elubeck/RoboScope2/PipetRobot/pipettorUpsideDown.png

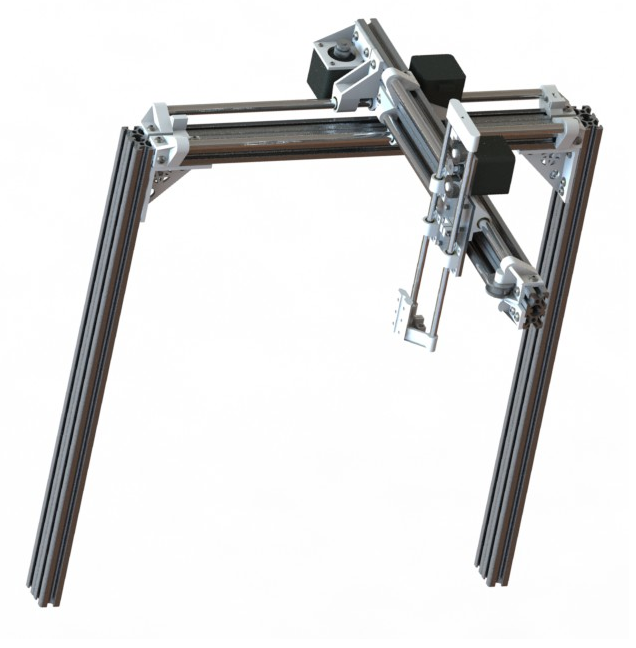
PipetRobot/pipettorUpsideDown.png
