elubeck/RoboScope2/PipetRobot/upsideDown2.JPG

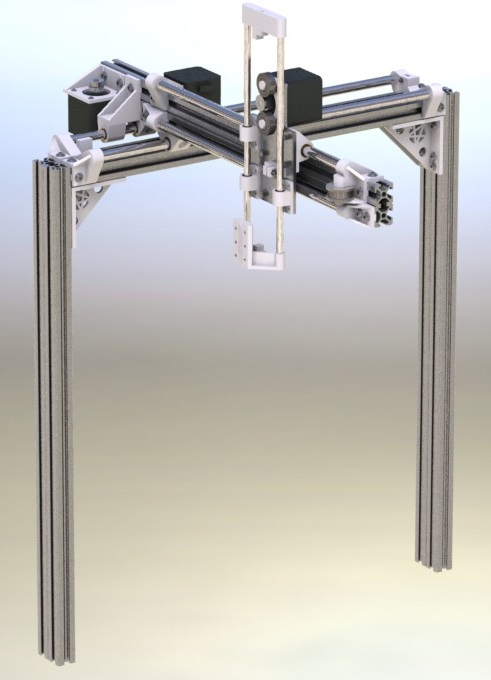
PipetRobot/upsideDown2.JPG
