elubeck/RoboScope2/PipetRobot/NeedleLuerHolder.sldasm

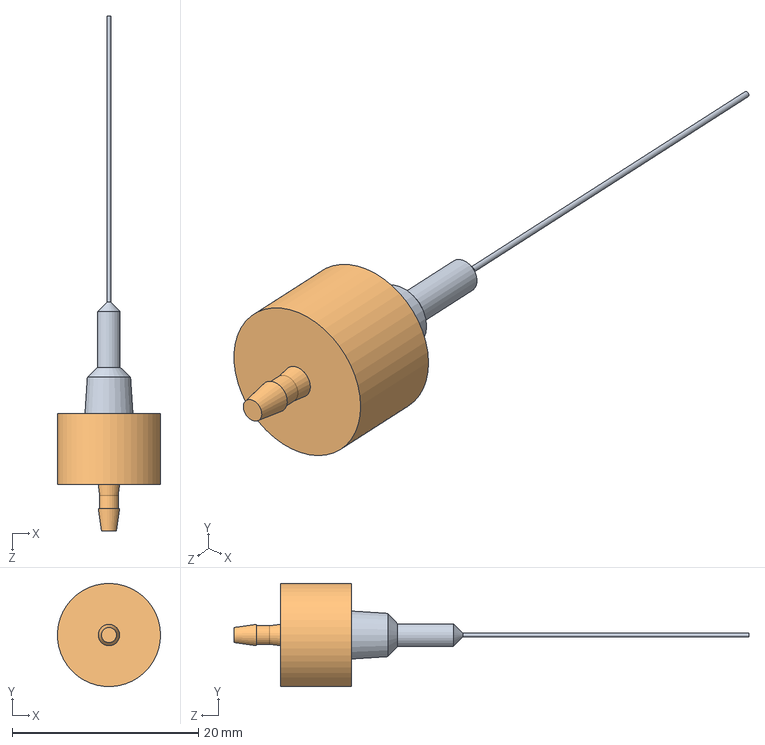
[picture p13: CAD file, 2014-07-27]
PipetRobot/NeedleLuerHolder.sldasm
11.1 x 11.1 x 55.3 mm
needleluer
needle
