elubeck/RoboScope2/PipetRobot/xaxisbearing.STL

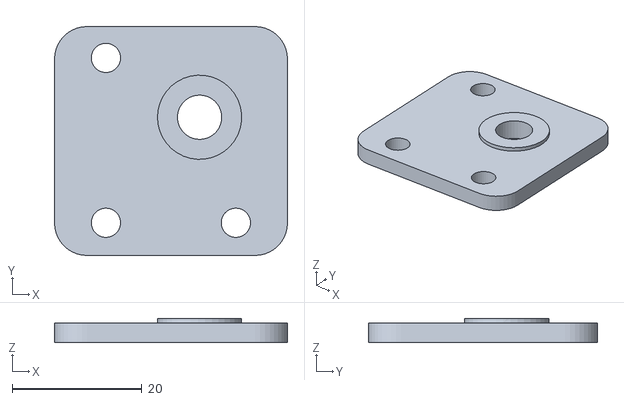
[picture p20: CAD file, 2014-07-27]
PipetRobot/xaxisbearing.STL
35.9 x 35.2 x 3.70
