elubeck/RoboScope2/PipetRobot/bearingmountflat.sldprt

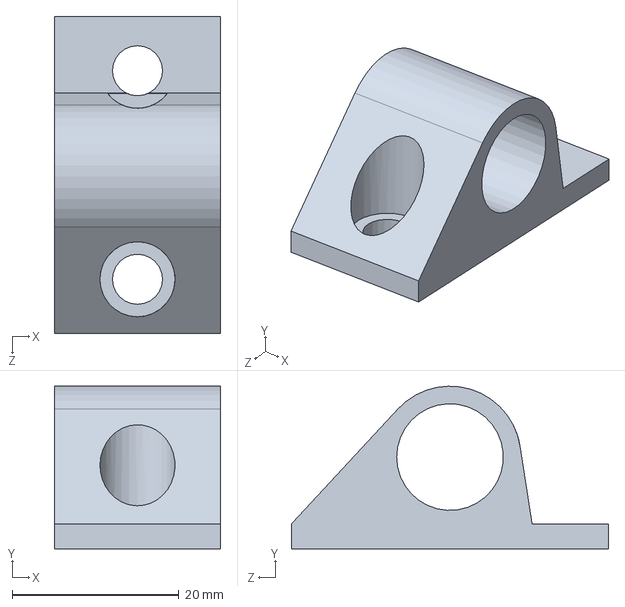
[picture p21: CAD file, 2014-07-27]
PipetRobot/bearingmountflat.sldprt
19.9 x 19.5 x 38.0 mm
