elubeck/RoboScope2/PipetRobot/syringe/syringeholderbottom.sldprt

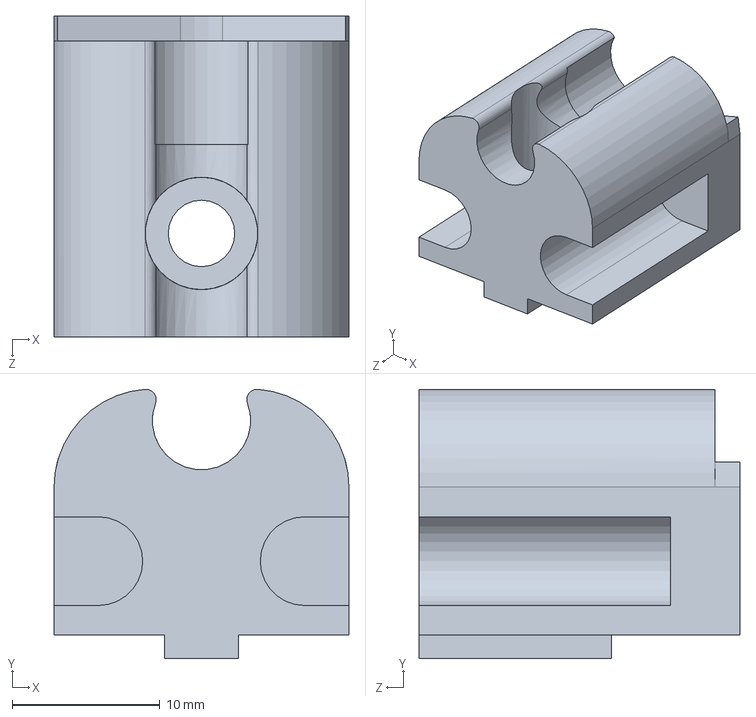
[picture p22: CAD file, 2014-07-27]
PipetRobot/syringe/syringeholderbottom.sldprt
20.0 x 18.2 x 21.7 mm
