elubeck/RoboScope2/PipetRobot/vialholder/bottle.SLDPRT

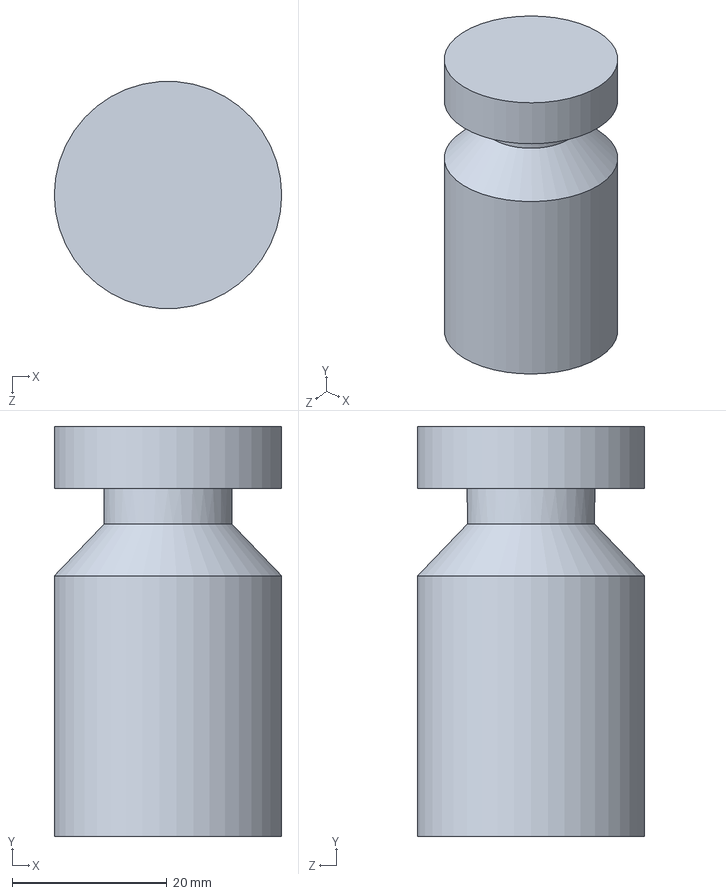
[picture p23: CAD file, 2014-07-27]
PipetRobot/vialholder/bottle.SLDPRT
29.4 x 53.0 x 29.3 mm
