elubeck/RoboScope2/PipetRobot/vialholder/vialrack.SLDPRT

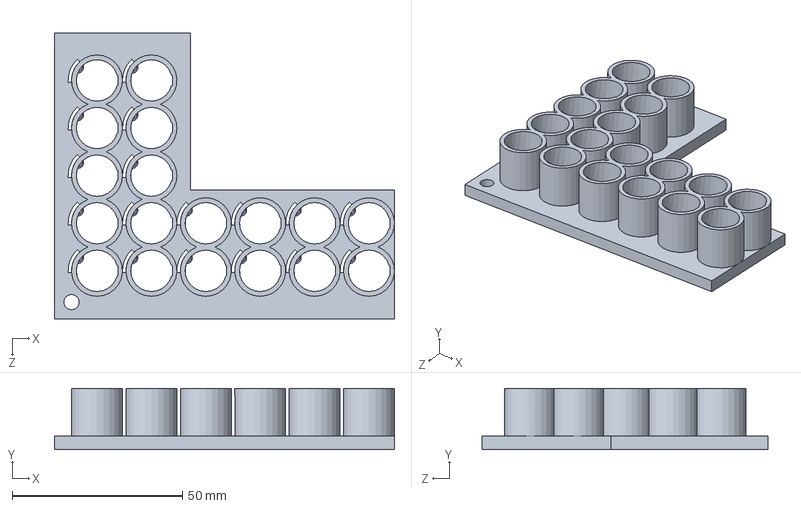
[picture p24: CAD file, 2014-07-27]
PipetRobot/vialholder/vialrack.SLDPRT
100.0 x 18.0 x 84.2 mm
