elubeck/RoboScope2/PipetRobot/syringe/plungerholder.STL

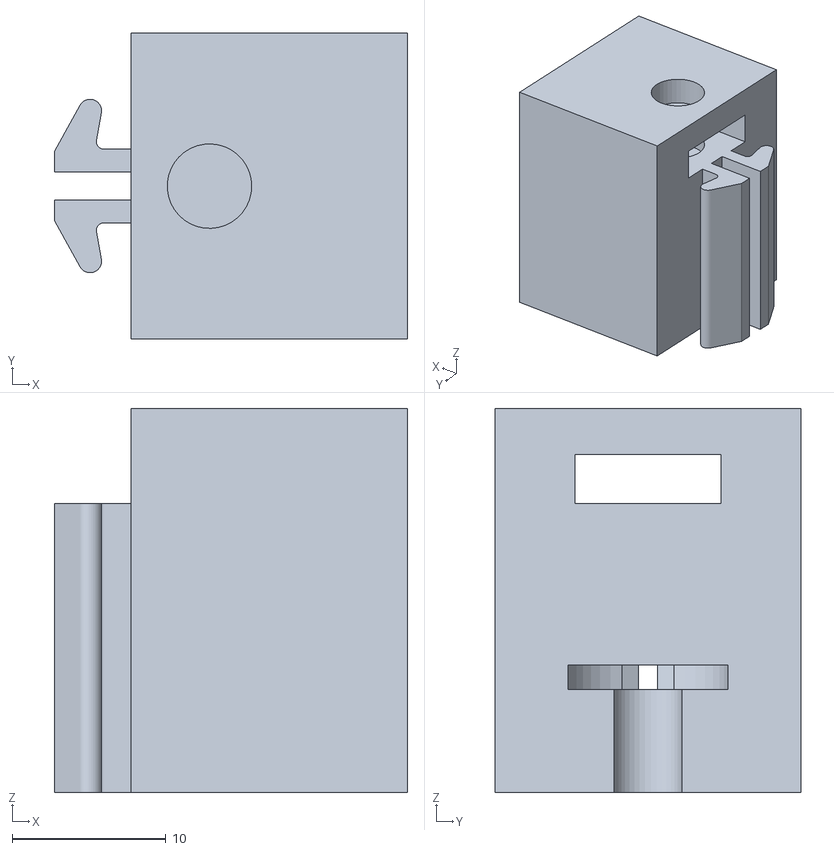
[picture p25: CAD file, 2014-07-27]
PipetRobot/syringe/plungerholder.STL
23.0 x 20.0 x 25.0
