elubeck/RoboScope2/PipetRobot/vialholder/bottlerack.SLDPRT

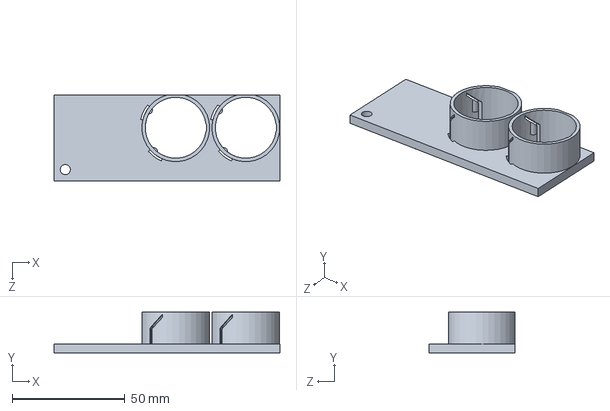
[picture p26: CAD file, 2014-07-27]
PipetRobot/vialholder/bottlerack.SLDPRT
100.0 x 18.0 x 38.0 mm
