elubeck/RoboScope2/PipetRobot/syringe/pistonholder.sldprt

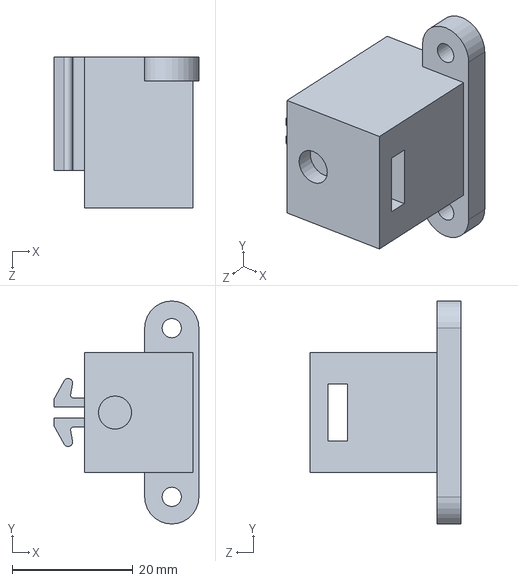
[picture p27: CAD file, 2014-07-27]
PipetRobot/syringe/pistonholder.sldprt
24.0 x 37.0 x 25.0 mm
