elubeck/RoboScope2/PipetRobot/vialholder/1_6mltube.SLDPRT

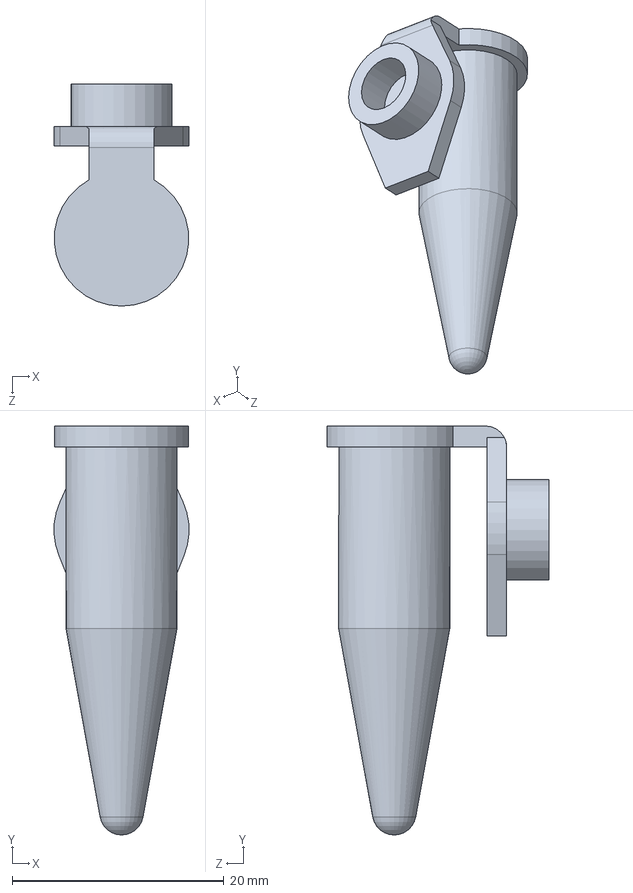
[picture p28: CAD file, 2014-07-27]
PipetRobot/vialholder/1_6mltube.SLDPRT
12.7 x 38.6 x 21.0 mm
