elubeck/RoboScope2/PipetRobot/CornerRodClampCutout.sldprt

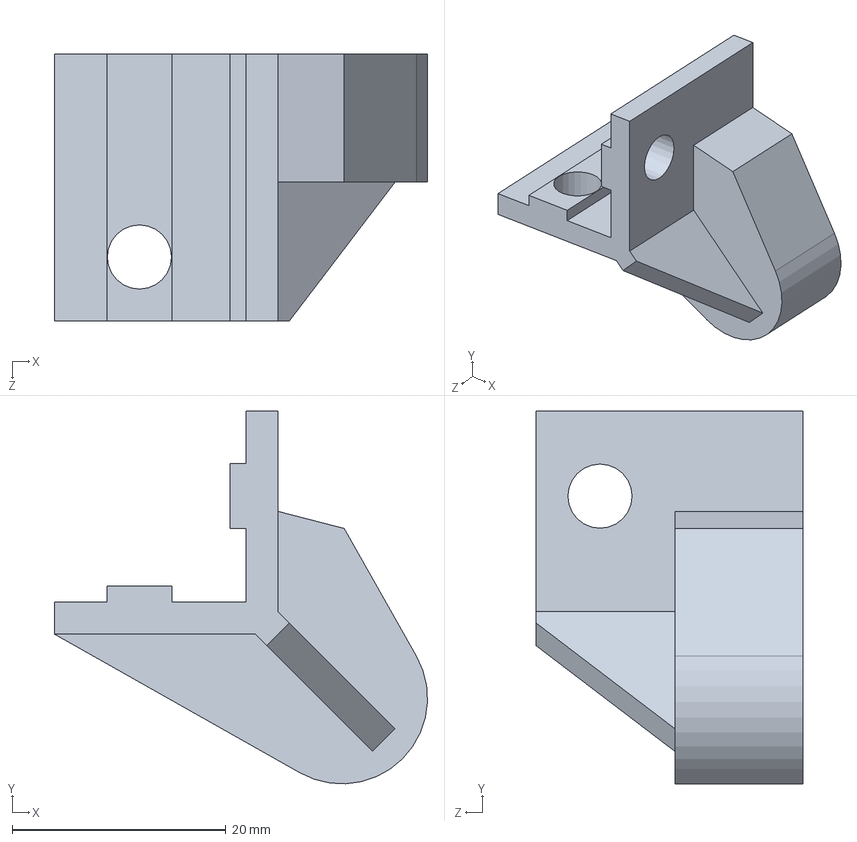
[picture p29: CAD file, 2014-07-27]
PipetRobot/CornerRodClampCutout.sldprt
34.9 x 34.8 x 25.0 mm
