elubeck/RoboScope2/PipetRobot/syringe/rodcoupler.sldprt

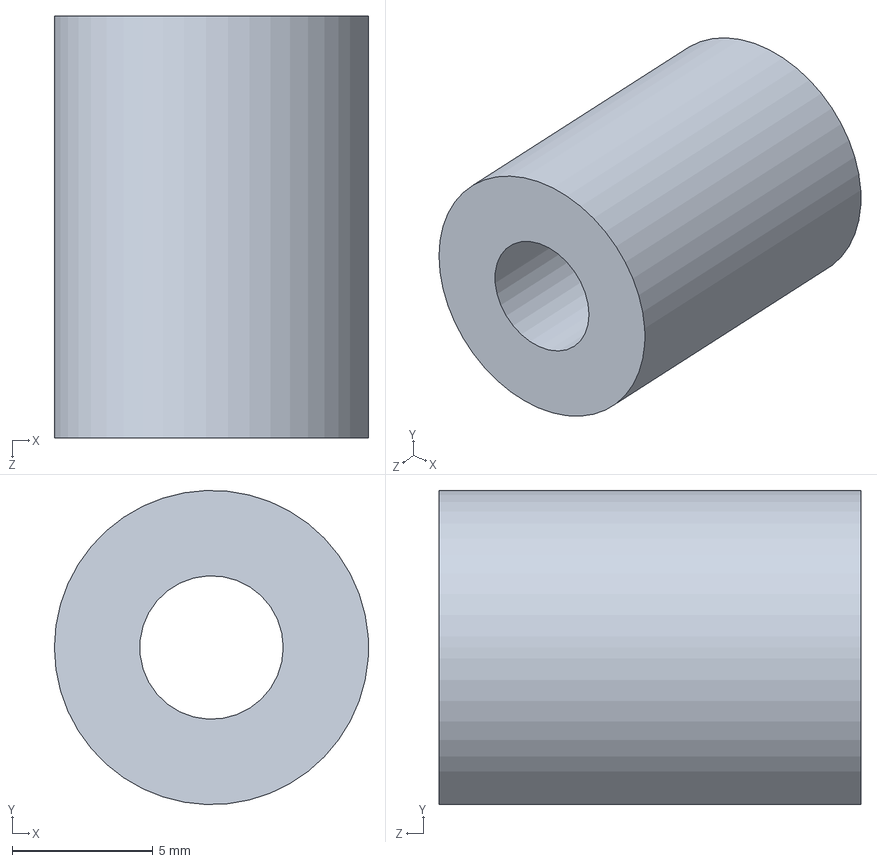
[picture p30: CAD file, 2014-07-27]
PipetRobot/syringe/rodcoupler.sldprt
11.2 x 11.2 x 15.0 mm
