elubeck/RoboScope2/PipetRobot/beltTrapTensioner2.sldprt

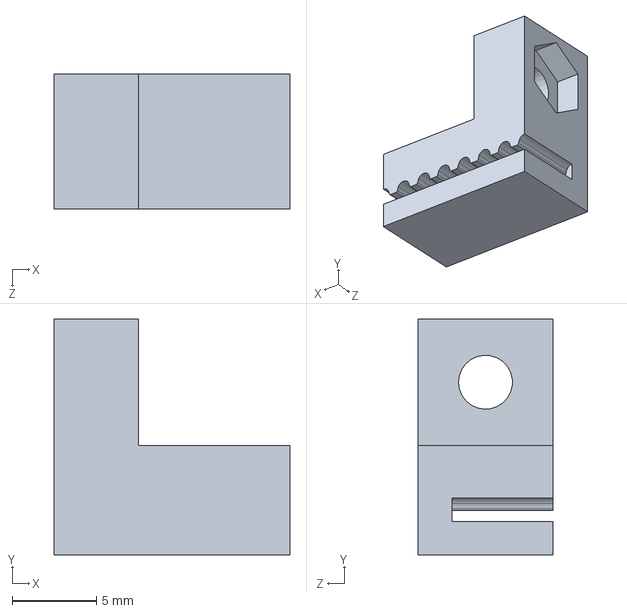
[picture p31: CAD file, 2014-07-27]
PipetRobot/beltTrapTensioner2.sldprt
14.0 x 14.0 x 8.00 mm
