elubeck/RoboScope2/PipetRobot/beltTrapmid.STL

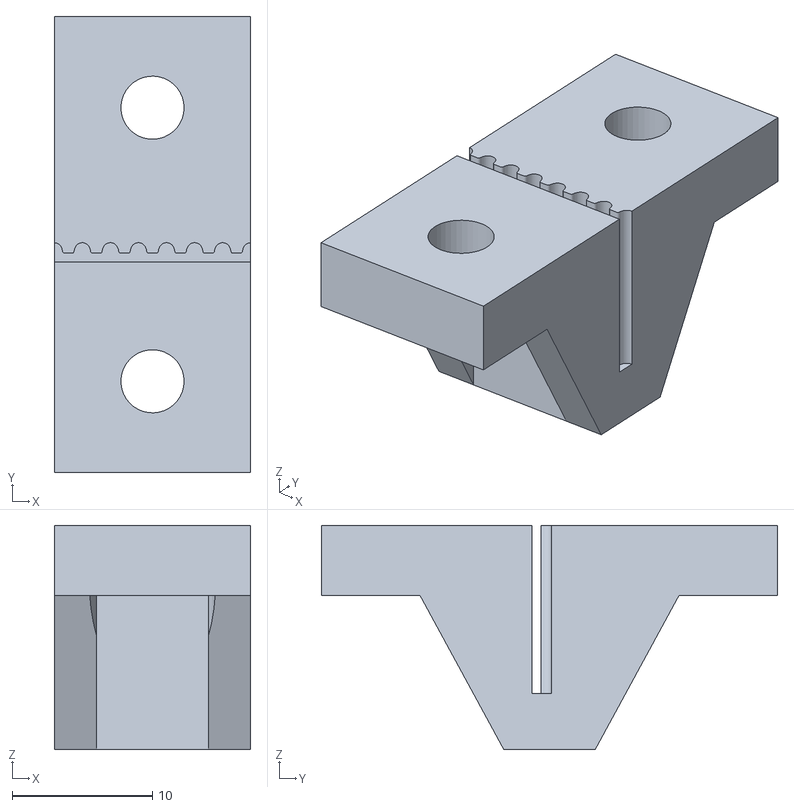
[picture p32: CAD file, 2014-07-27]
PipetRobot/beltTrapmid.STL
14.0 x 32.5 x 16.0
