elubeck/RoboScope2/PipetRobot/syringe/syringeplunger.SLDPRT

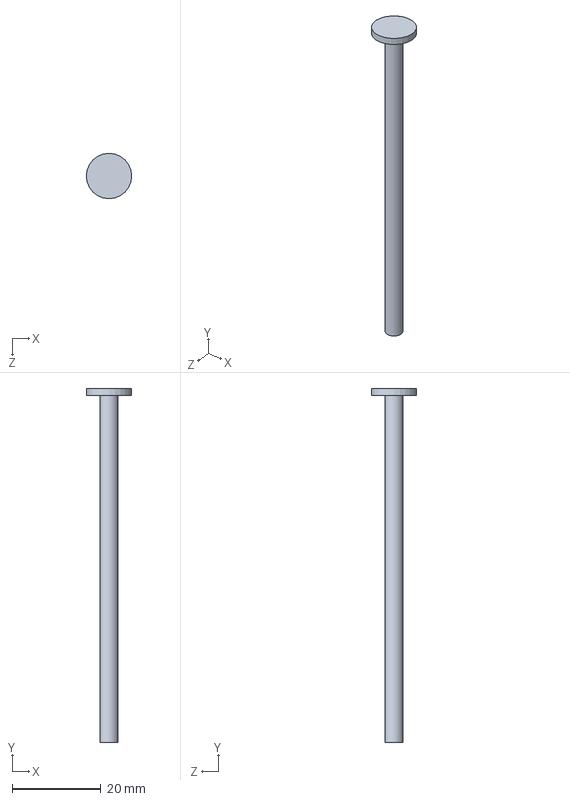
[picture p33: CAD file, 2014-07-27]
PipetRobot/syringe/syringeplunger.SLDPRT
10.2 x 79.6 x 10.2 mm
