elubeck/RoboScope2/PipetRobot/AluminumExtrusion.sldprt

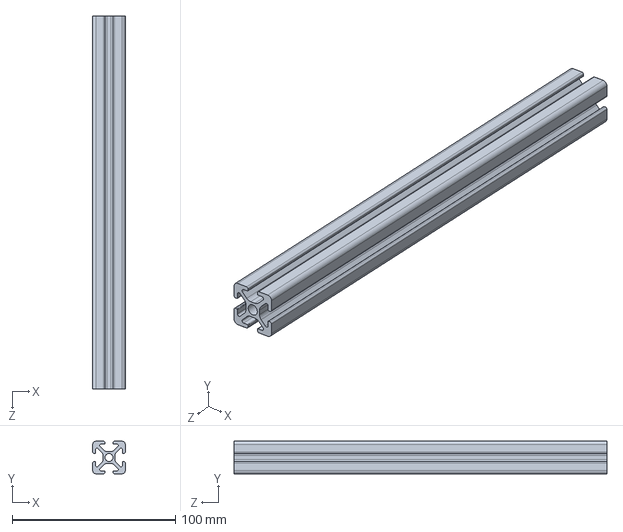
[picture p34: CAD file, 2014-07-27]
PipetRobot/AluminumExtrusion.sldprt
20.0 x 20.0 x 228.6 mm
