elubeck/RoboScope2/PipetRobot/syringe/needleluer.SLDPRT

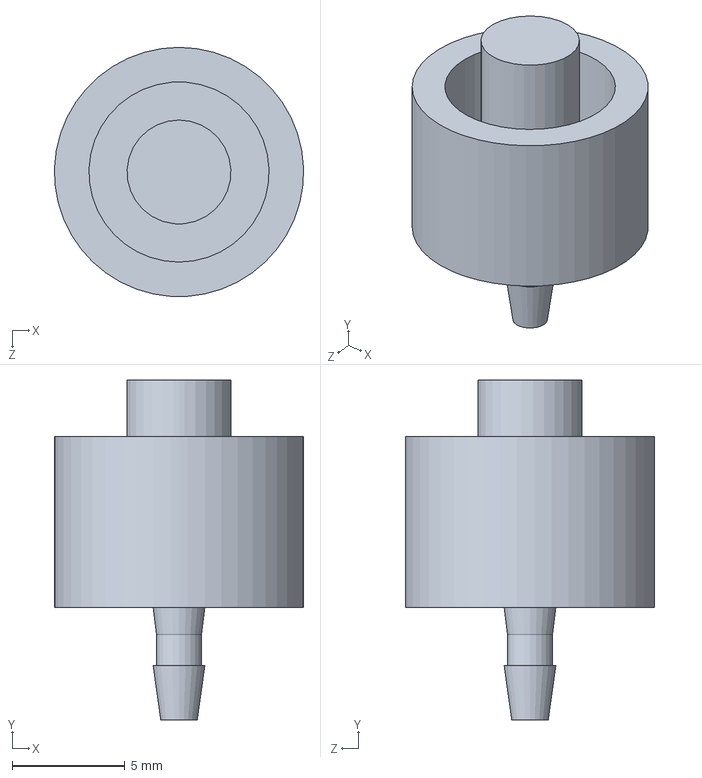
[picture p35: CAD file, 2014-07-27]
PipetRobot/syringe/needleluer.SLDPRT
11.1 x 15.1 x 11.1 mm
