elubeck/RoboScope2/PipetRobot/syringe/syringeclamper.sldprt

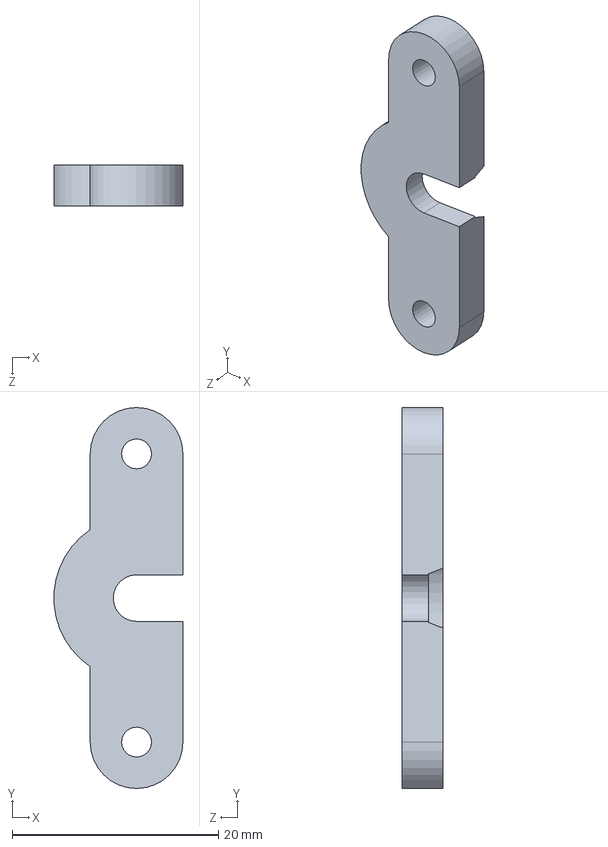
[picture p36: CAD file, 2014-07-27]
PipetRobot/syringe/syringeclamper.sldprt
12.5 x 37.0 x 4.00 mm
