elubeck/RoboScope2/PipetRobot/pulleymount.STL

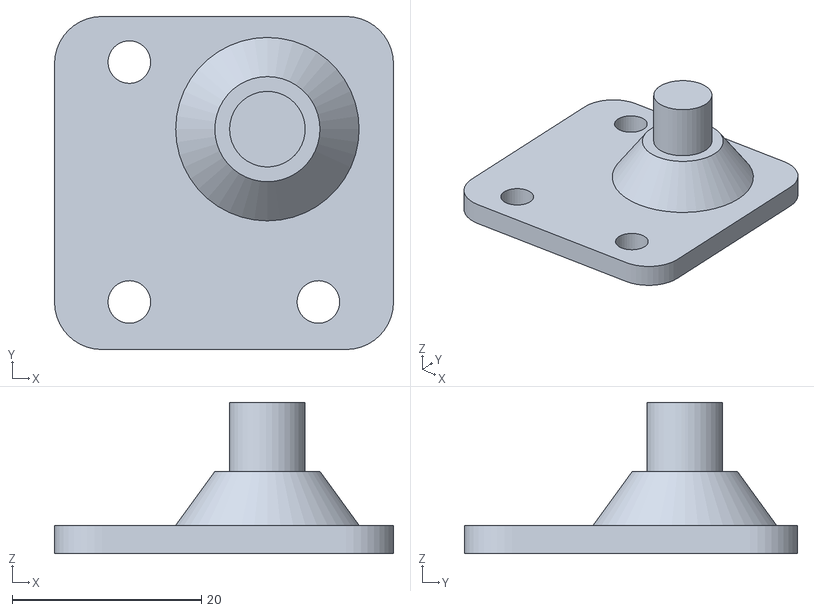
[picture p37: CAD file, 2014-07-27]
PipetRobot/pulleymount.STL
35.9 x 35.2 x 16.0
