elubeck/RoboScope2/PipetRobot/syringe/1mlsyringe.sldprt

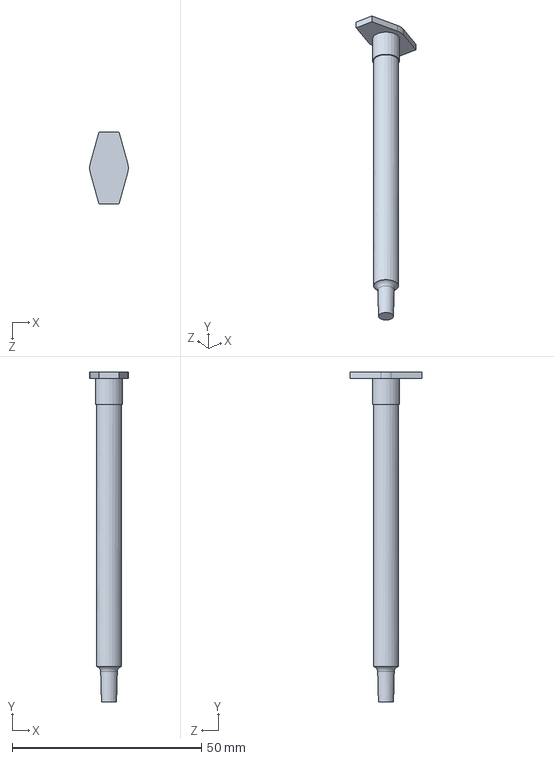
[picture p38: CAD file, 2014-07-27]
PipetRobot/syringe/1mlsyringe.sldprt
10.2 x 87.1 x 19.0 mm
