elubeck/RoboScope2/PipetRobot/syringe/syringeholdertop.sldprt

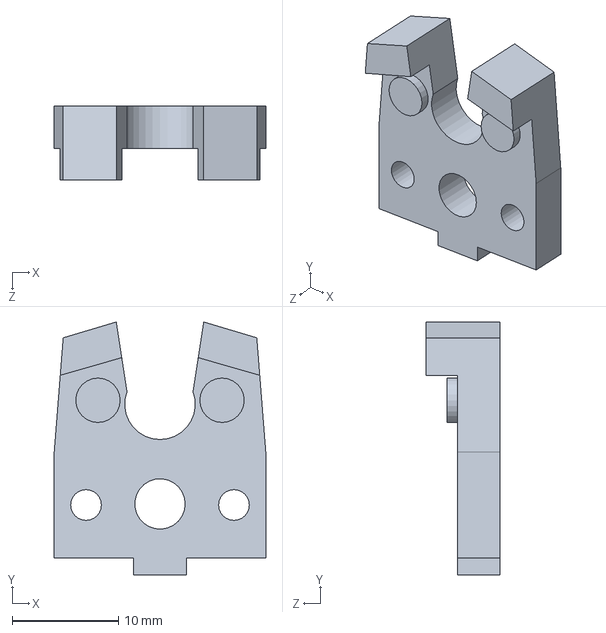
[picture p39: CAD file, 2014-07-27]
PipetRobot/syringe/syringeholdertop.sldprt
20.0 x 23.9 x 7.00 mm
