elubeck/RoboScope2/PipetRobot/beltTrapTensioner.sldprt

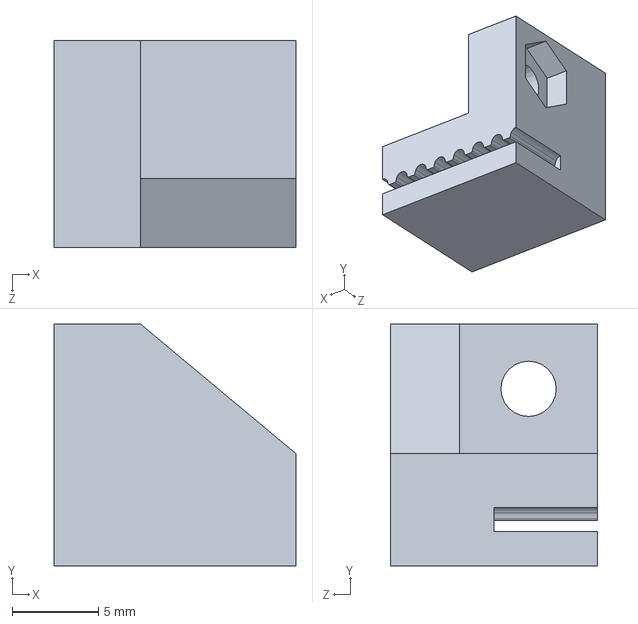
[picture p40: CAD file, 2014-07-27]
PipetRobot/beltTrapTensioner.sldprt
14.0 x 14.0 x 12.0 mm
