elubeck/RoboScope2/PipetRobot/syringe/needle.SLDPRT

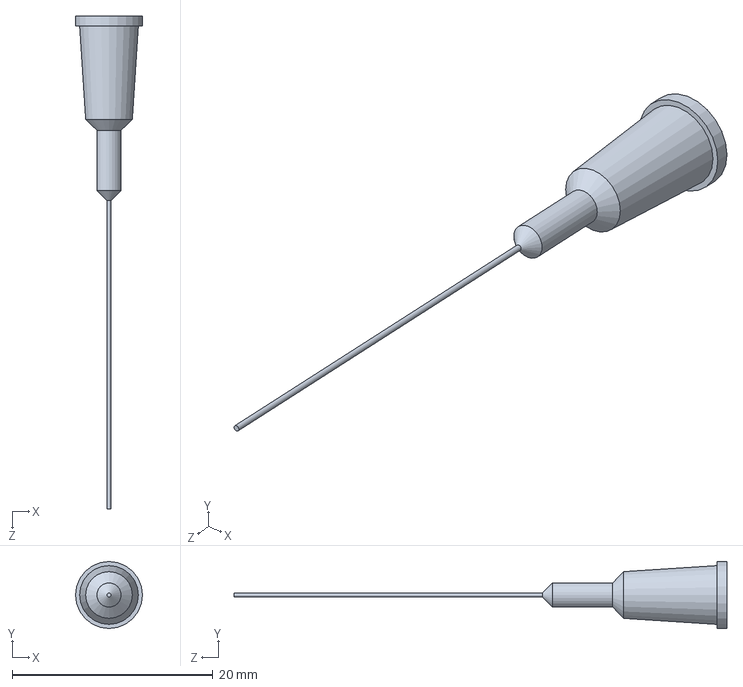
[picture p41: CAD file, 2014-07-27]
PipetRobot/syringe/needle.SLDPRT
6.67 x 6.67 x 49.1 mm
