elubeck/RoboScope2/PipetRobot/zsyringemount.sldprt

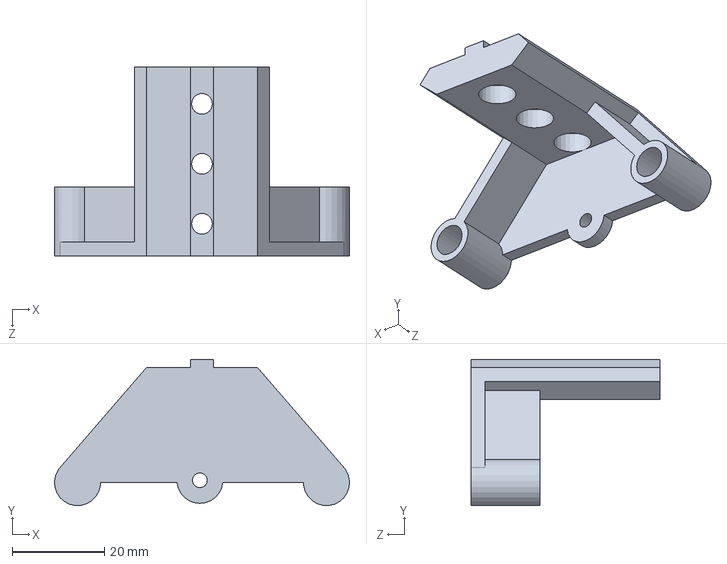
[picture p42: CAD file, 2014-07-27]
PipetRobot/zsyringemount.sldprt
64.0 x 31.7 x 41.0 mm
