elubeck/RoboScope2/PipetRobot/rainP200.SLDPRT

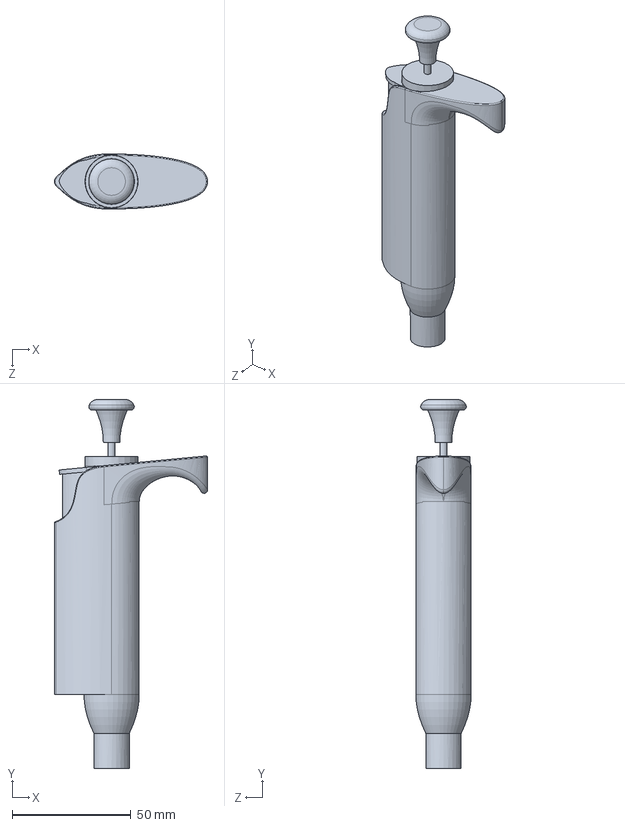
[picture p43: CAD file, 2014-07-27]
PipetRobot/rainP200.SLDPRT
64.5 x 155.2 x 23.3 mm
