elubeck/RoboScope2/PipetRobot/syringe/qiagen_purple_column.SLDPRT

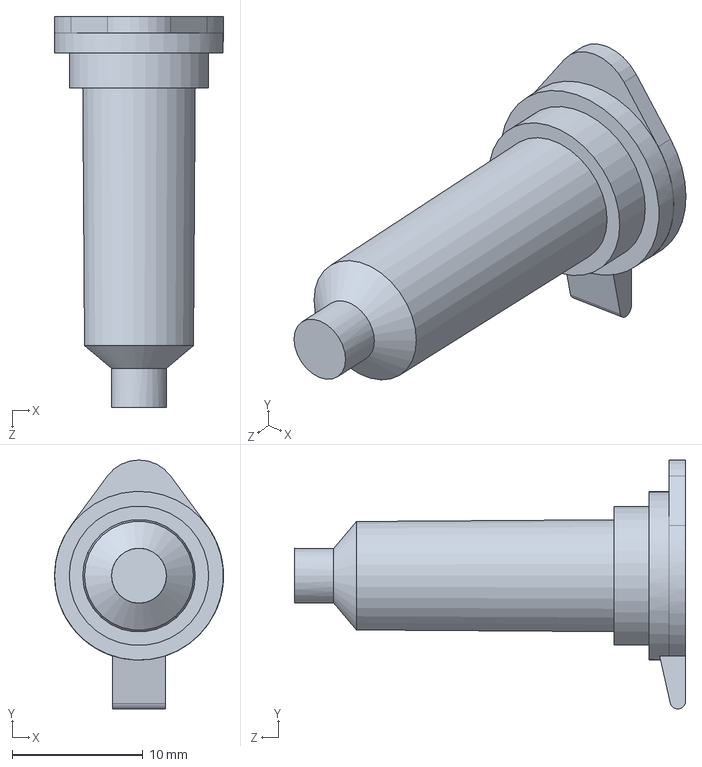
[picture p44: CAD file, 2014-07-27]
PipetRobot/syringe/qiagen_purple_column.SLDPRT
12.9 x 19.0 x 29.9 mm
