elubeck/RoboScope2/PipetRobot/bearingmount.sldprt

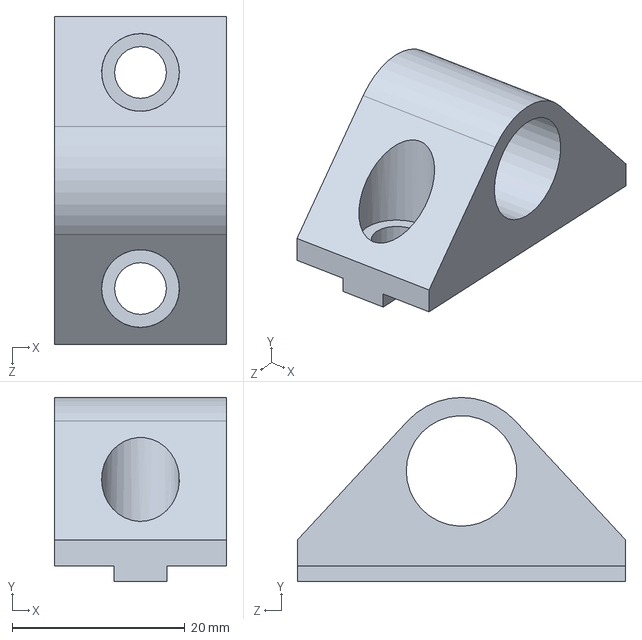
[picture p45: CAD file, 2014-07-27]
PipetRobot/bearingmount.sldprt
19.9 x 21.3 x 38.0 mm
