elubeck/RoboScope2/PipetRobot/epP200.SLDPRT

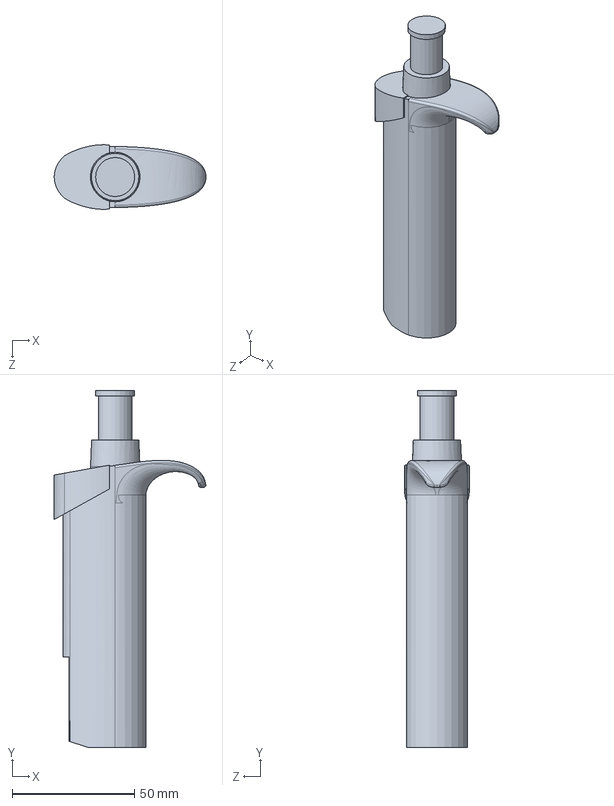
[picture p46: CAD file, 2014-07-27]
PipetRobot/epP200.SLDPRT
62.0 x 146.0 x 26.4 mm
