elubeck/RoboScope2/PipetRobot/ThreeEighthsRod.sldprt

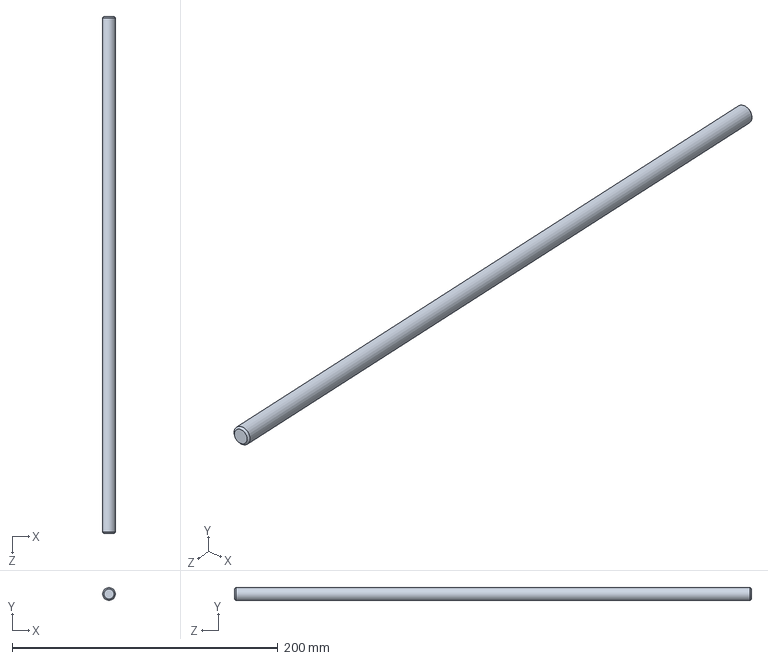
[picture p47: CAD file, 2014-07-27]
PipetRobot/ThreeEighthsRod.sldprt
9.65 x 9.65 x 389.0 mm
